WARMW00D/HUD-Audi-A4-B9-MLB-Evo-ESP32-S3-SuperMini-LCD-2.79-NV3007-BLE/schematics/HUD_supermini_NV3007_rev2_DCDC.png

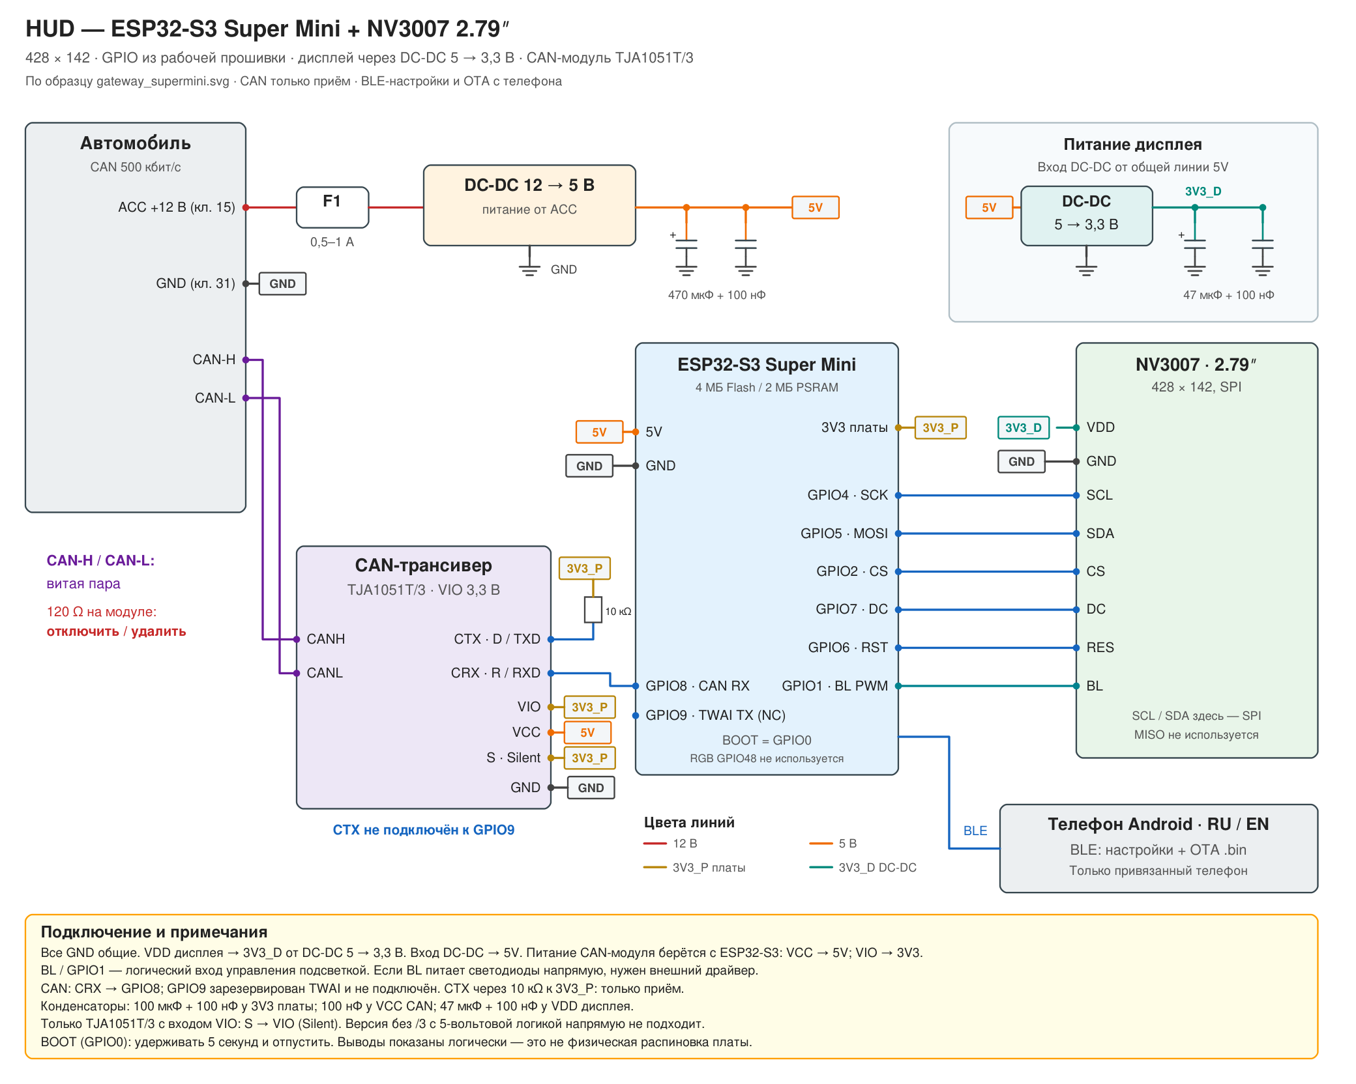
schematics/HUD_supermini_NV3007_rev2_DCDC.png
