WARMW00D/HUD-Audi-A4-B9-MLB-Evo-ESP32-S3-SuperMini-LCD-2.79-NV3007-BLE/supermini_hud/hud_ble_ota.h

#pragma once
#include <stdint.h>
class NimBLEServer;
typedef bool (*HudOtaAuthorize)(uint16_t handle);
void hud_ble_ota_begin(NimBLEServer *server, HudOtaAuthorize authorize);
void hud_ble_ota_disconnect(uint16_t handle);
void hud_ble_ota_poll();
bool hud_ble_ota_busy();
