WARMW00D/HUD-Audi-A4-B9-MLB-Evo-ESP32-S3-SuperMini-LCD-2.79-NV3007-BLE/supermini_hud/hud_log.cpp

#include <Arduino.h>
#include <stdarg.h>
#include <stdio.h>
#include "hud_log.h"

void hud_log_write(const char *s) { Serial.print(s); }
void arduino_printf(const char *format, ...)
{
    char buf[256];
    va_list args;
    va_start(args, format);
    vsnprintf(buf, sizeof(buf), format, args);
    va_end(args);
    hud_log_write(buf);
}
